kholia/Easy-Field-Strength-Meter/Simulations/Screenshot_2022-01-05_14-53-18.png

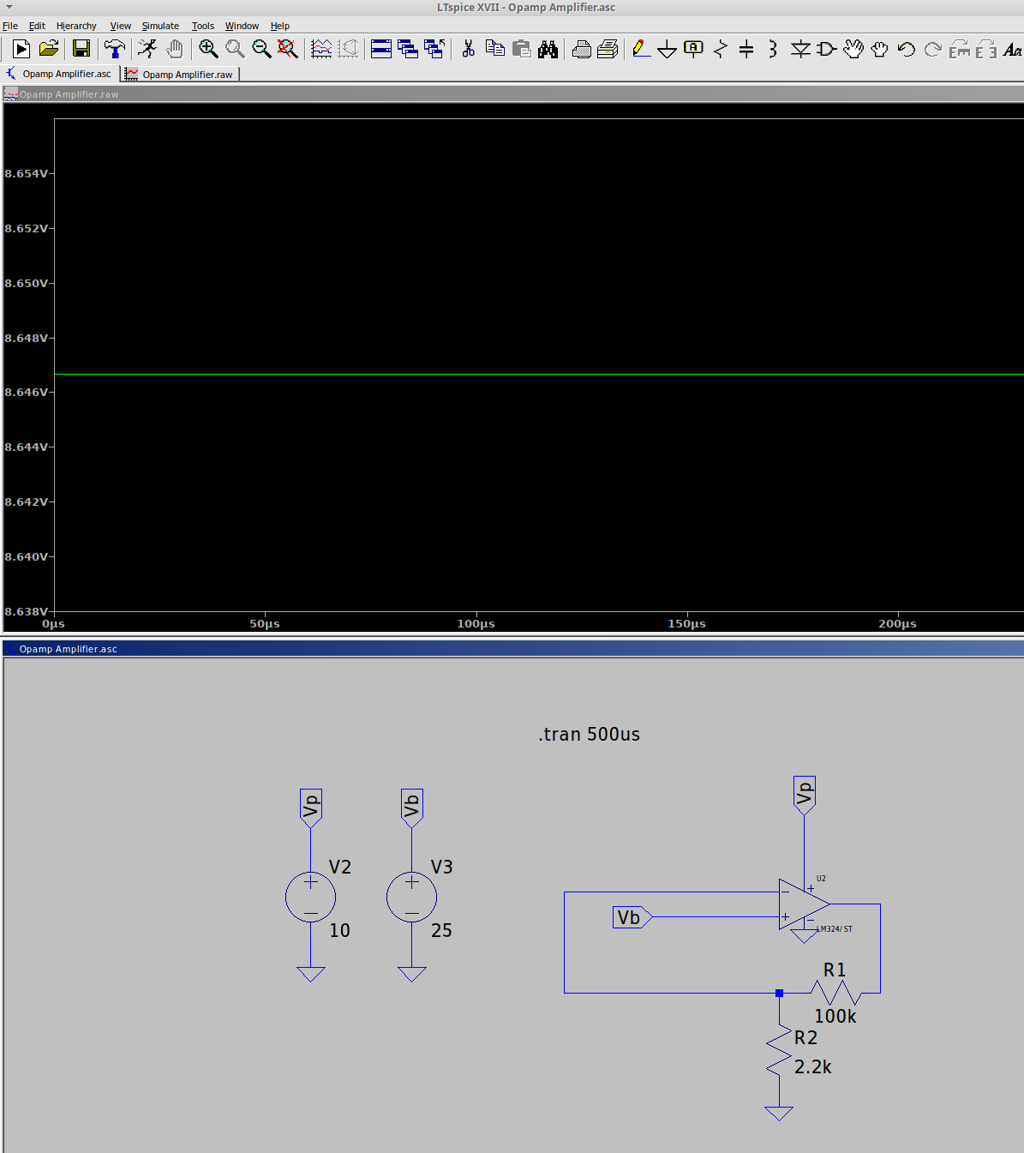
Simulations/Screenshot_2022-01-05_14-53-18.png
