kholia/Easy-Field-Strength-Meter/images/Sample-BOM-Radio-Prepper-Screenshot_2021-07-10_10-03-00.png

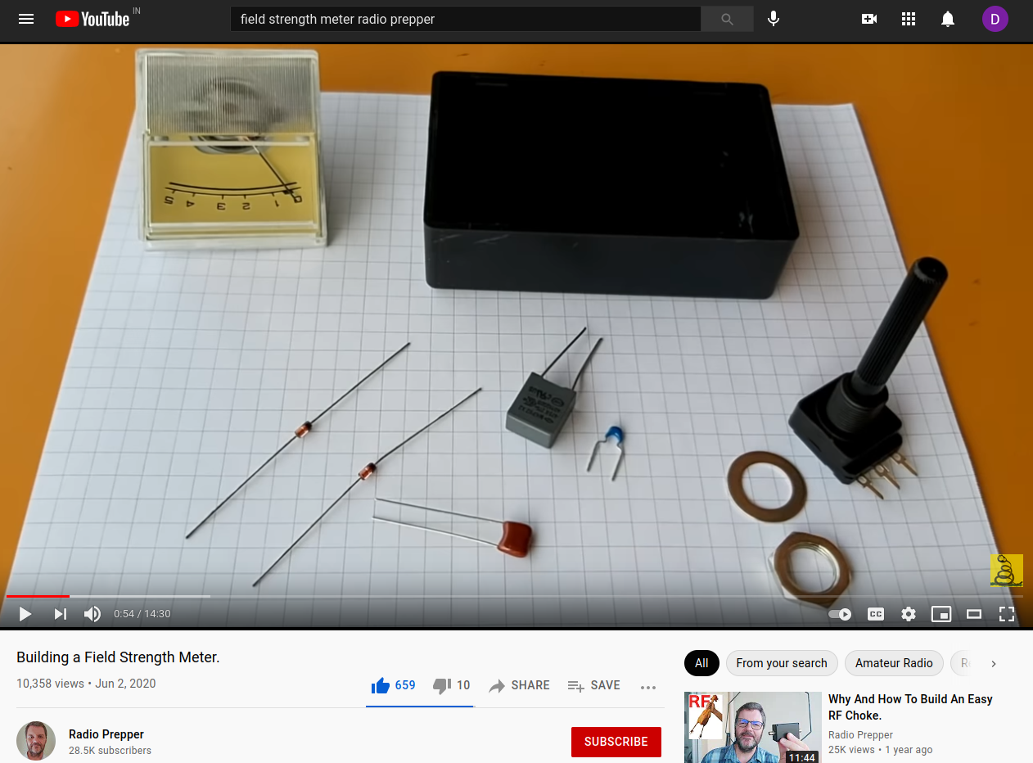
images/Sample-BOM-Radio-Prepper-Screenshot_2021-07-10_10-03-00.png
