kholia/Easy-Field-Strength-Meter/Simulations/Opamp Amplifier.asc

R1: res; 100k
R2: res; 2.2k
U2: LM324_ST
V2: voltage; 10
V3: voltage; 0.01
Named nets: Vb, 0, Vp
.tran 500us
